abbttls/GlowBlaster/assets/IMG_7176.JPEG

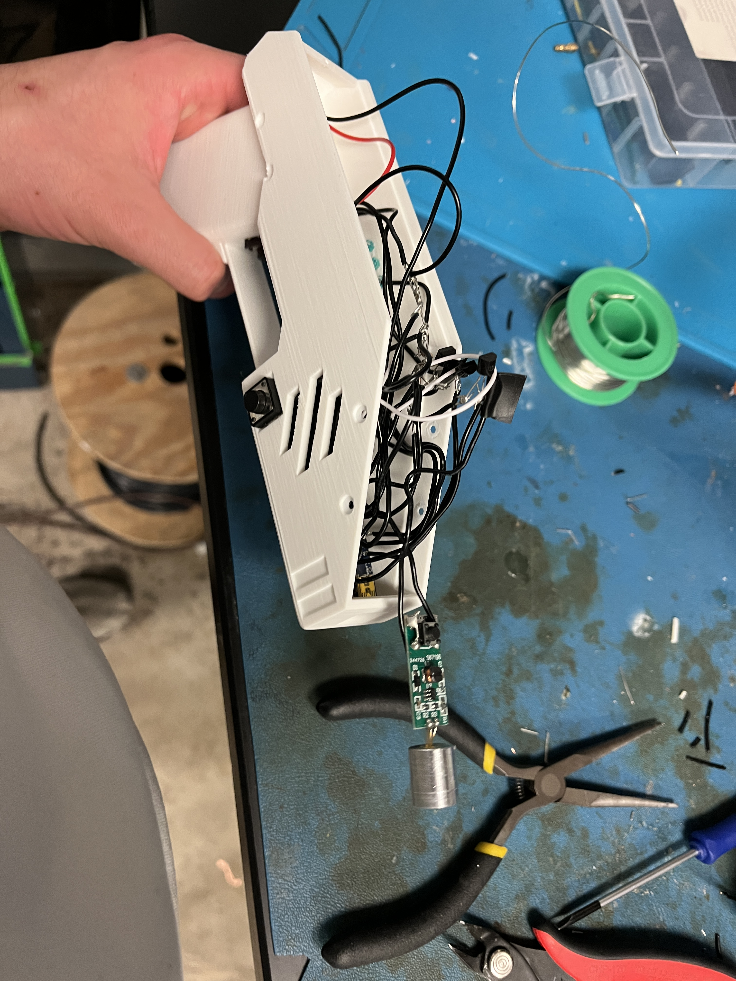
assets/IMG_7176.JPEG
